OlexOlex/TPE-Module/Hardware+Chassis/Pictures/IMG_20160629_231217.jpg

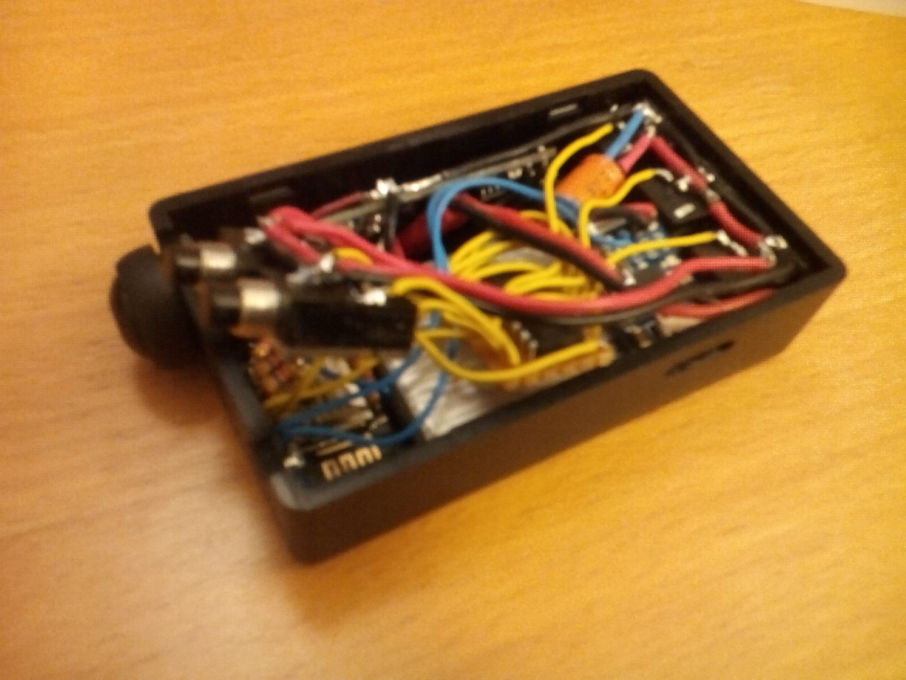
Hardware+Chassis/Pictures/IMG_20160629_231217.jpg
