OlexOlex/TPE-Module/Hardware+Chassis/Pictures/IMG_20160630_000944.jpg

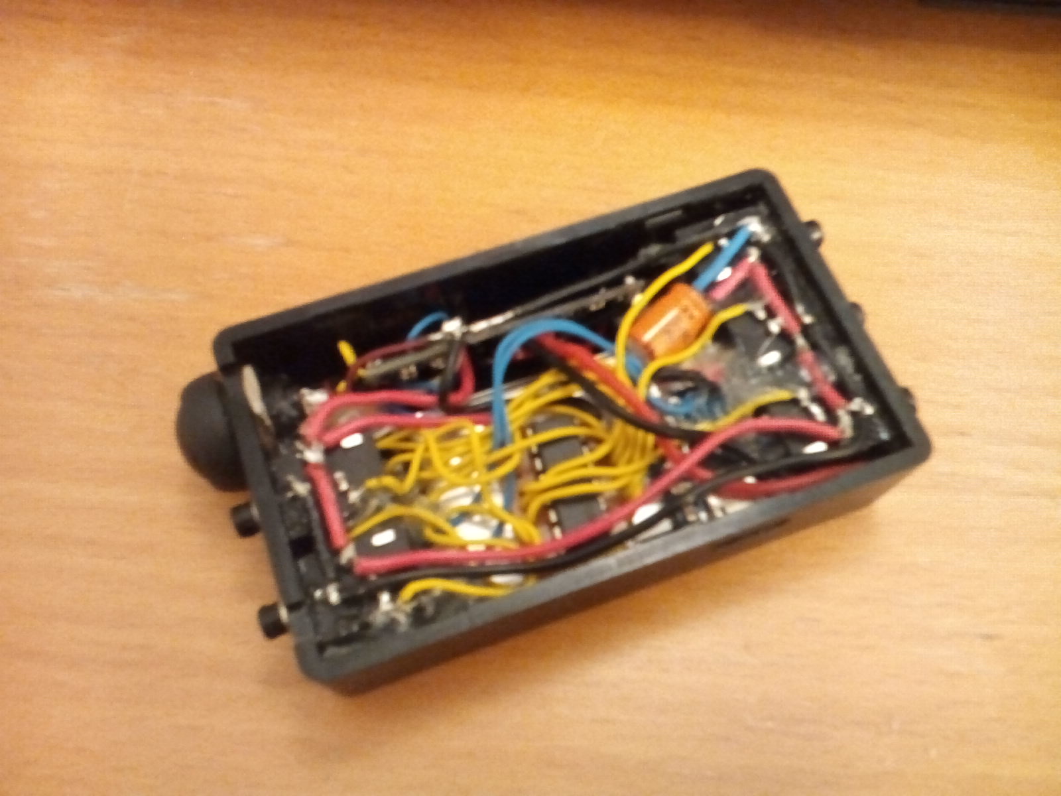
Hardware+Chassis/Pictures/IMG_20160630_000944.jpg
