OlexOlex/TPE-Module/Hardware+Chassis/Pictures/IMG_20160630_032400.jpg

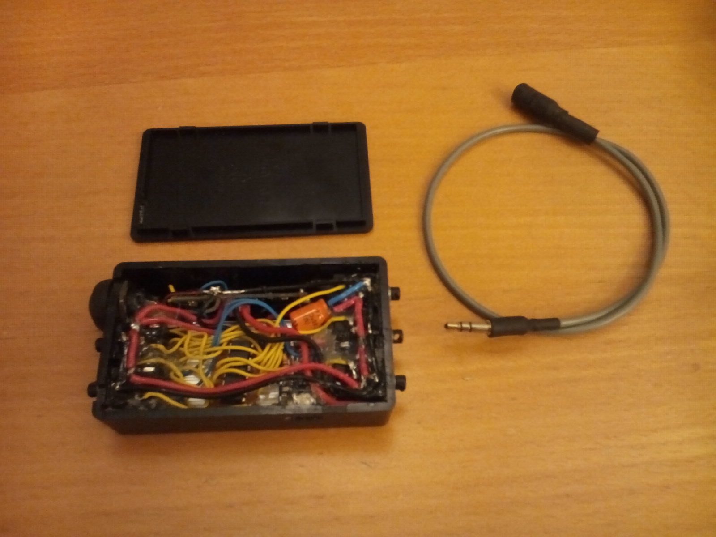
Hardware+Chassis/Pictures/IMG_20160630_032400.jpg
