OlexOlex/TPE-Module/Hardware+Chassis/Pictures/IMG_20160630_033355.jpg

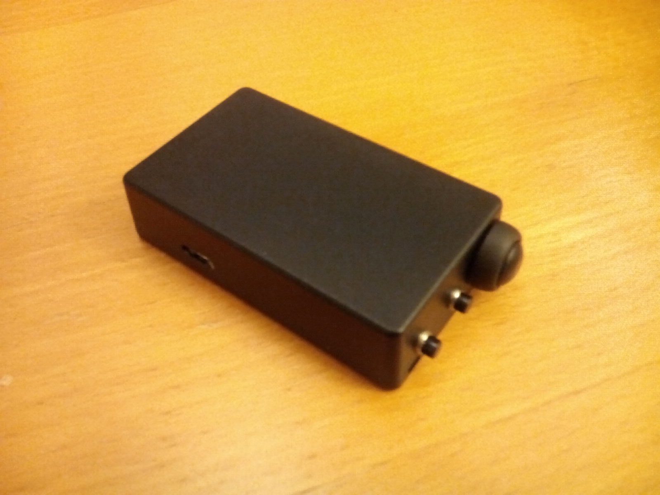
Hardware+Chassis/Pictures/IMG_20160630_033355.jpg
