OlexOlex/TPE-Module/Hardware+Chassis/Pictures/IMG_20160630_033415.jpg

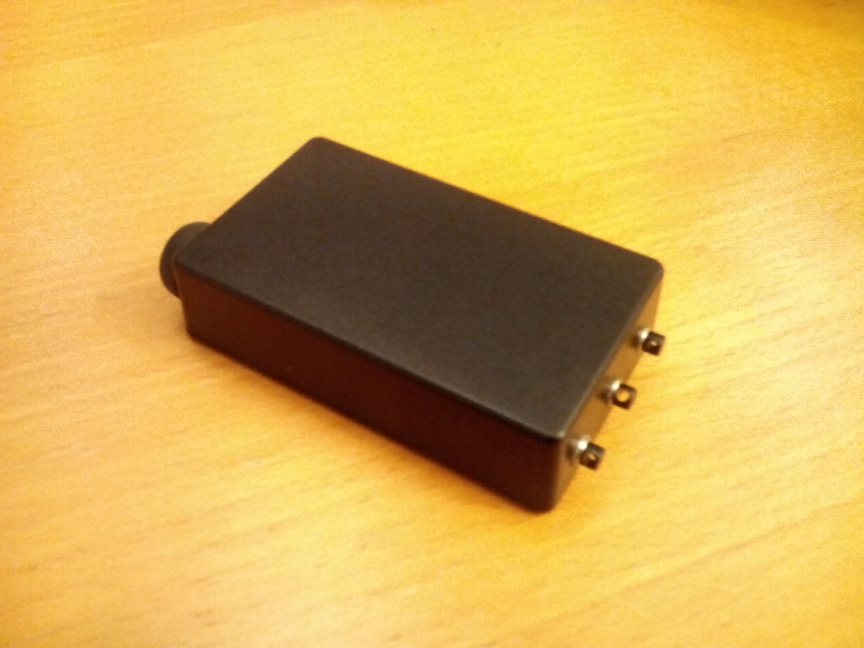
Hardware+Chassis/Pictures/IMG_20160630_033415.jpg
