OlexOlex/TPE-Module/Software/Pictures/English_website_status_v1.0.png

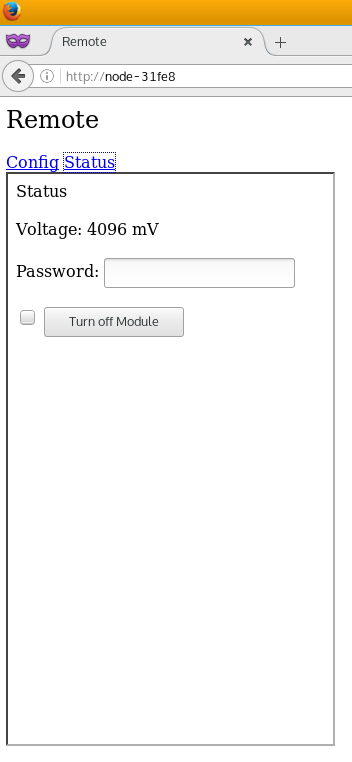
Software/Pictures/English_website_status_v1.0.png
