OlexOlex/TPE-Module/Software/Pictures/German_website_v1.0/Statusseite.png

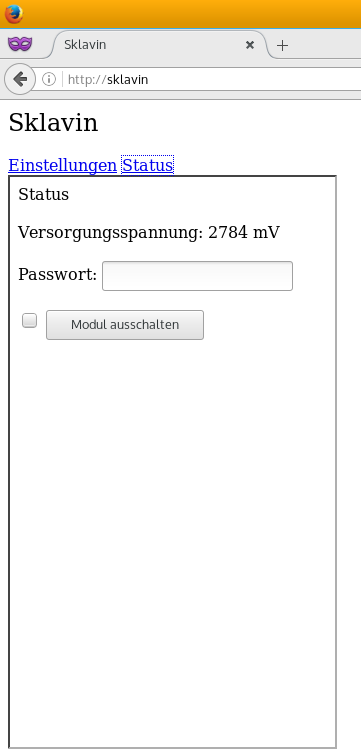
Software/Pictures/German_website_v1.0/Statusseite.png
